Electrochalanes/ELECTROCHALANESWRONACIONAL2025FE/src/Diagrama de Flujo para Desafío Abierto.png

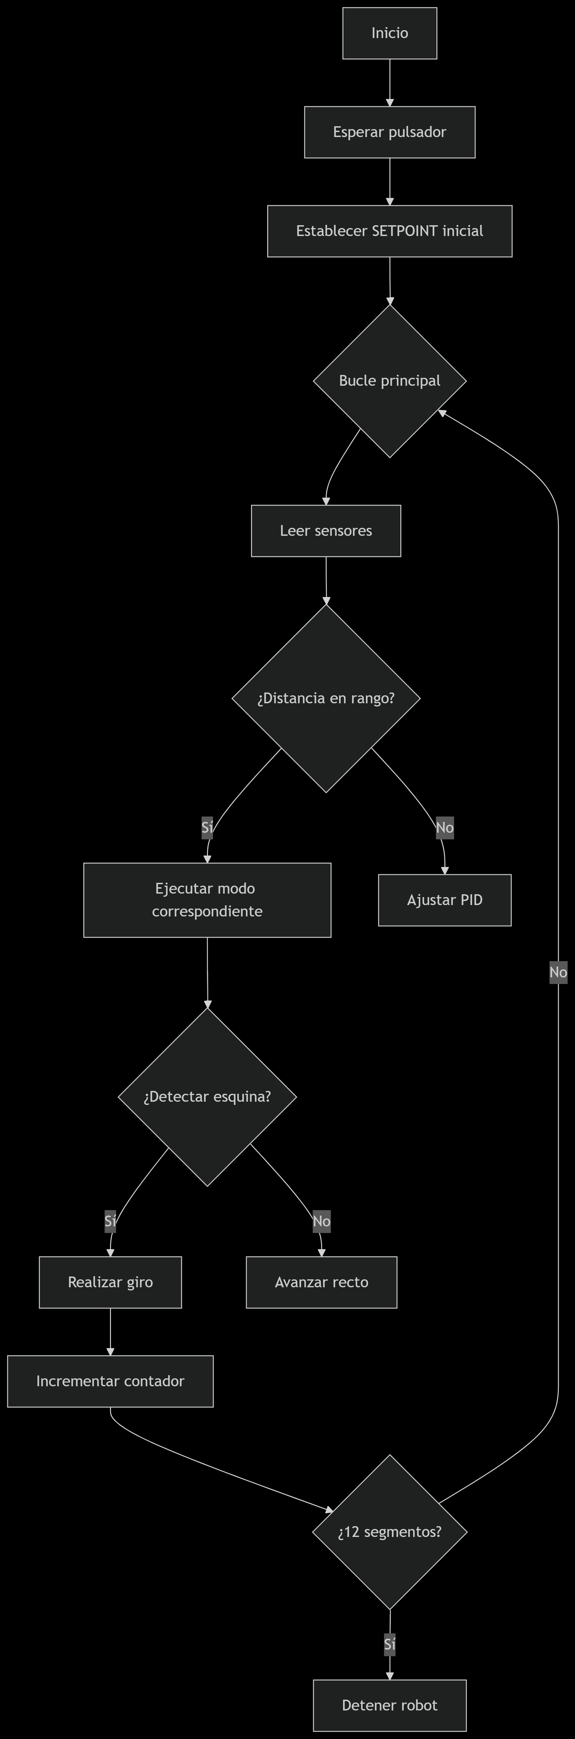
src/Diagrama de Flujo para Desafío Abierto.png
