Electrochalanes/ELECTROCHALANESWRONACIONAL2025FE/v-photos/WRO DERECHA.jpg

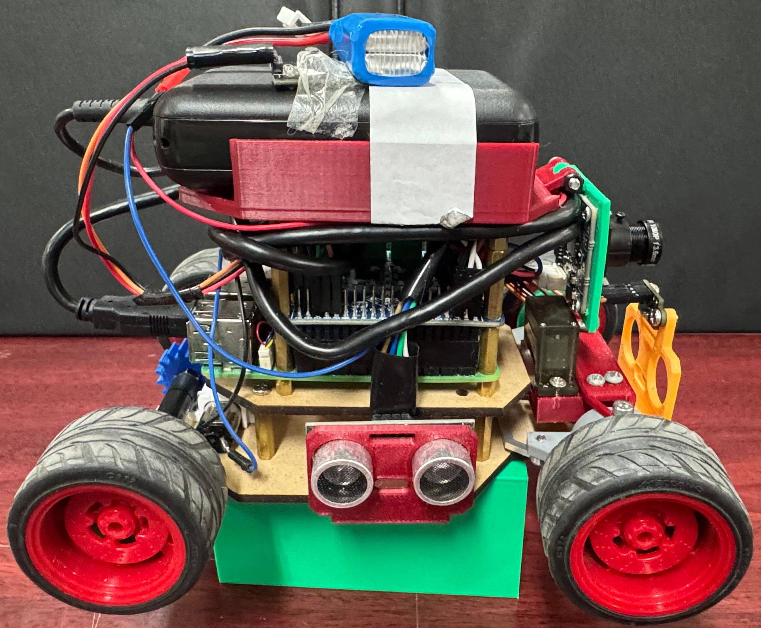
v-photos/WRO DERECHA.jpg
