Electrochalanes/ELECTROCHALANESWRONACIONAL2025FE/v-photos/WRO FRONTAL.jpg

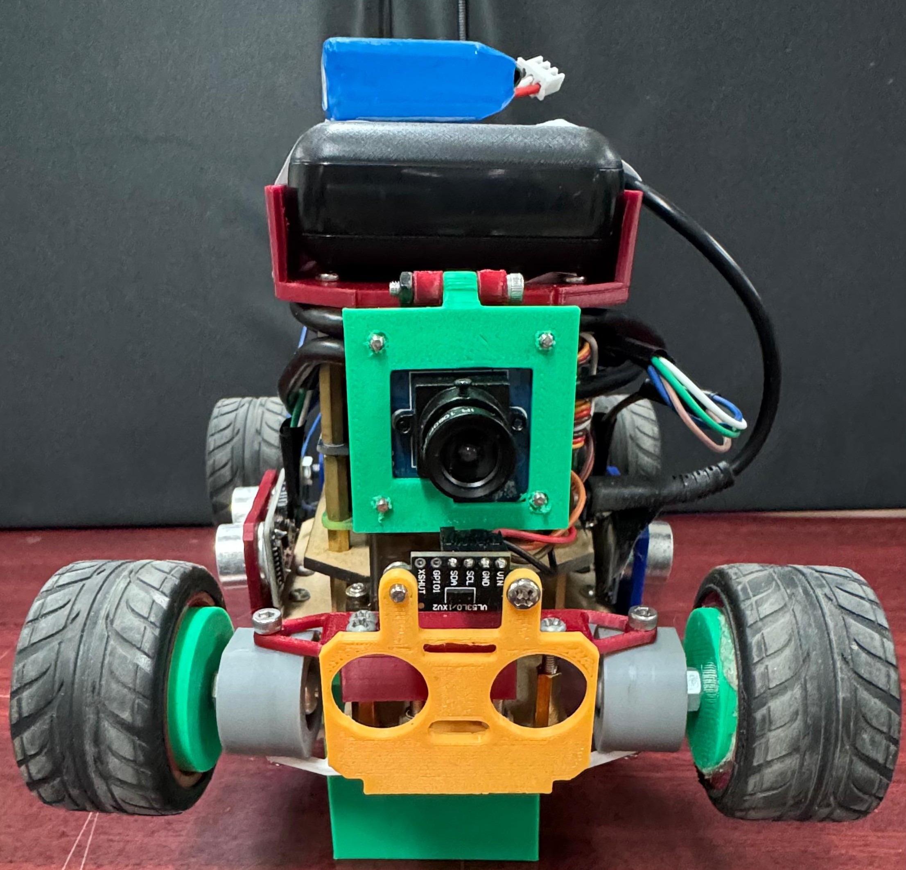
v-photos/WRO FRONTAL.jpg
