Electrochalanes/ELECTROCHALANESWRONACIONAL2025FE/v-photos/WRO IZQUIERDA.jpg

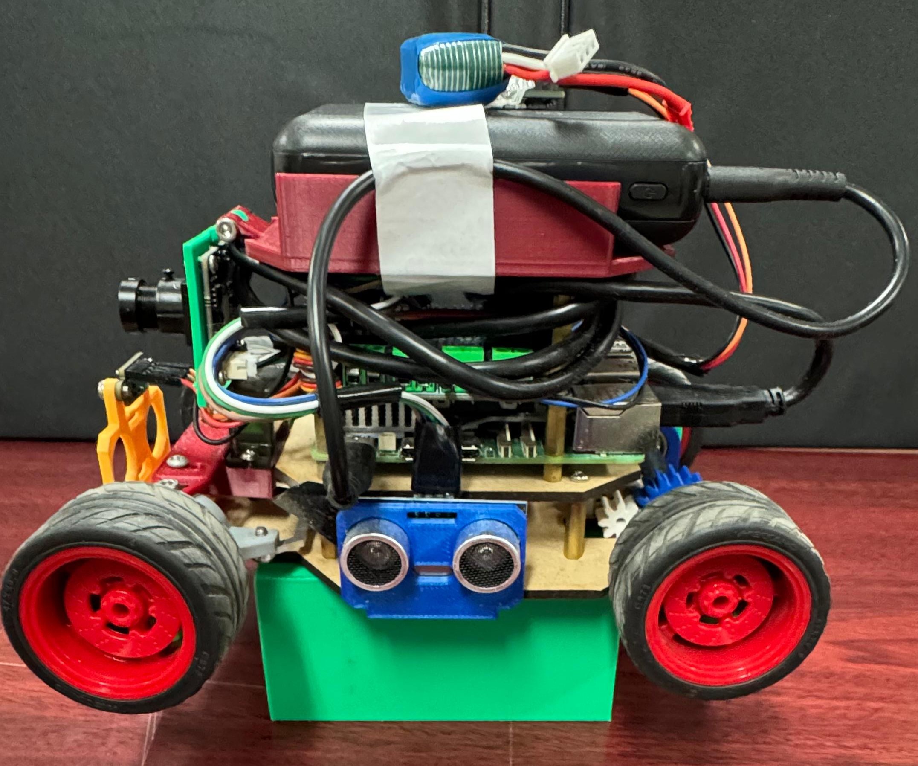
v-photos/WRO IZQUIERDA.jpg
