Electrochalanes/ELECTROCHALANESWRONACIONAL2025FE/v-photos/WRO TRASERO.jpg

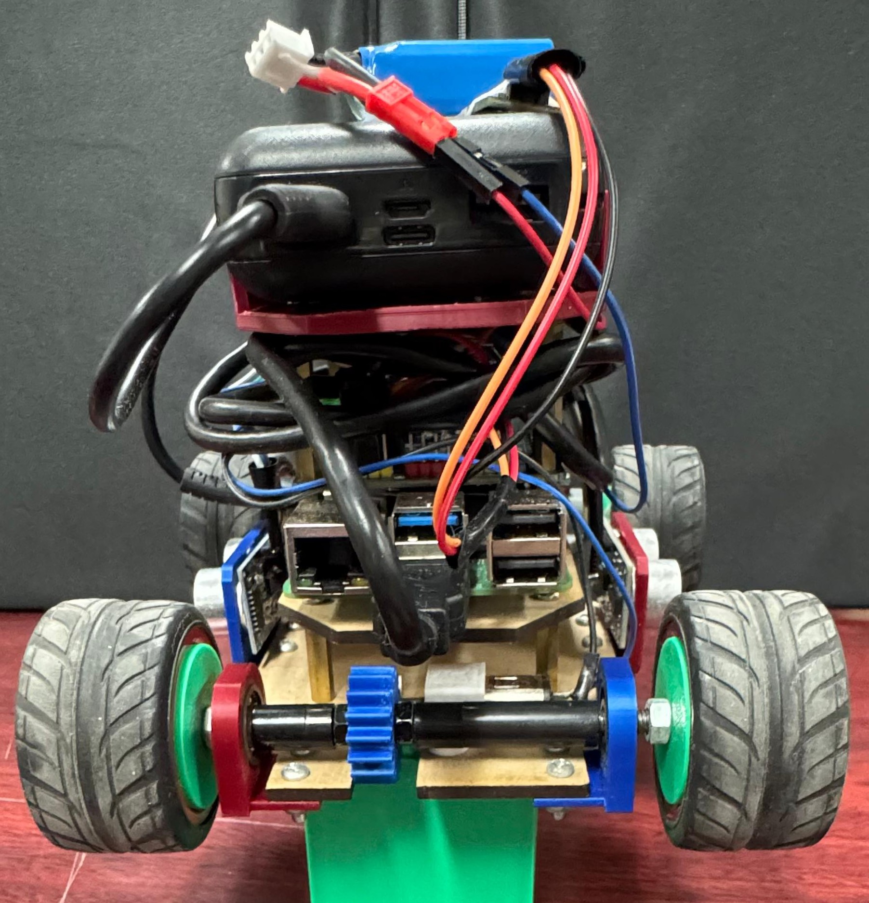
v-photos/WRO TRASERO.jpg
